krystofh/kitchen_timer/src/tones.h

#ifndef TONES_H
#define TONES_H

// Define frequencies for standard musical notes
// Octave numbers refer to scientific pitch notation (e.g., A4 = 440 Hz)

// C notes
#define C1  33
#define C2  65
#define C3  131
#define C4  262
#define C5  523
#define C6  1047
#define C7  2093
#define C8  4186

// C# / Db notes
#define CS1 35
#define CS2 69
#define CS3 139
#define CS4 277
#define CS5 554
#define CS6 1109
#define CS7 2217
#define CS8 4435

// D notes
#define D1  37
#define D2  73
#define D3  147
#define D4  294
#define D5  587
#define D6  1175
#define D7  2349
#define D8  4699

// D# / Eb notes
#define DS1 39
#define DS2  78
#define DS3  156
#define DS4  311
#define DS5  622
#define DS6  1245
#define DS7  2489
#define DS8  4978

// E notes
#define E1  41
#define E2  82
#define E3  165
#define E4  330
#define E5  659
#define E6  1319
#define E7  2637
#define E8  5274

// F notes
#define F1  44
#define F2  87
#define F3  175
#define F4  349
#define F5  698
#define F6  1397
#define F7  2794
#define F8  5588

// F# / Gb notes
#define FS1  46
#define FS2  92
#define FS3  185
#define FS4  370
#define FS5  740
#define FS6  1480
#define FS7  2960
#define FS8  5920

// G notes
#define G1  49
#define G2  98
#define G3  196
#define G4  392
#define G5  784
#define G6  1568
#define G7  3136
#define G8  6272

// G# / Ab notes
#define GS1  52
#define GS2  104
#define GS3  208
#define GS4  415
#define GS5  831
#define GS6  1661
#define GS7  3322
#define GS8  6645

// A notes
#define A1  55
#define A2  110
#define A3  220
#define A4  440
#define A5  880
#define A6  1760
#define A7  3520
#define A8  7040

// A# / Bb notes
#define AS1  58
#define AS2  116
#define AS3  233
#define AS4  466
#define AS5  932
#define AS6  1865
#define AS7  3729
#define AS8  7459

// B notes
#define B1  62
#define B2  123
#define B3  247
#define B4  494
#define B5  988
#define B6  1976
#define B7  3951
#define B8  7902

#endif // TONES_H
